sparkfun/SparkFun_DataLogger_IoT_9DoF/Examples/Hardware_Tests/05_MAX17048/05_MAX17048.ino

// SparkFun DataLogger IoT – 9DoF Test Example
// Tested with Espressif ESP32 v2.0.5 and the "ESP32 Dev Module" board definition

/**********************************************************************************************
 *
 * WARNING!
 * 
 * This is a sketch we wrote to test the DataLogger IoT – 9DoF hardware.
 * Please think very carefully before uploading it to your DataLogger.
 * 
 * You will overwrite the DataLogger firmware, leaving it unable to update or restore itself. 
 * 
 * The DataLogger IoT – 9DoF comes pre-programmed with amazing firmware which can do _so_ much.
 * It is designed to be able to update itself and restore itself if necessary.
 * But it can not do that if you overwrite the firmware with this test sketch.
 * It is just like erasing the restore partition on your computer hard drive.
 * Do not do it - unless you really know what you are doing.
 * 
 * Really. We mean it.
 * 
 * Your friends at SparkFun.
 * 
 * License: MIT. Please see LICENSE.MD for more details
 * 
 **********************************************************************************************/

#include <Wire.h> // Needed for I2C

#include <SparkFun_MAX1704x_Fuel_Gauge_Arduino_Library.h> // Click here to get the library: http://librarymanager/All#SparkFun_MAX1704x_Fuel_Gauge_Arduino_Library

SFE_MAX1704X lipo(MAX1704X_MAX17048); // Create a MAX17048

void setup()
{
	Serial.begin(115200); // Start serial, to output debug data
  while (!Serial)
    ; //Wait for user to open terminal
  Serial.println(F("MAX17048 Example"));

  Wire.begin();

  lipo.enableDebugging(); // Uncomment this line to enable helpful debug messages on Serial

  // Set up the MAX17048 LiPo fuel gauge:
  if (lipo.begin() == false) // Connect to the MAX17048 using the default wire port
  {
    Serial.println(F("MAX17048 not detected. Please check wiring. Freezing."));
    while (1)
      ;
  }

  // Just because we can, let's reset the MAX17048
  Serial.println(F("Resetting the MAX17048..."));
  delay(1000); // Give it time to get its act back together

  // Read and print the reset indicator
  Serial.print(F("Reset Indicator was: "));
  bool RI = lipo.isReset(true); // Read the RI flag and clear it automatically if it is set
  Serial.println(RI); // Print the RI
  // If RI was set, check it is now clear
  if (RI)
  {
    Serial.print(F("Reset Indicator is now: "));
    RI = lipo.isReset(); // Read the RI flag
    Serial.println(RI); // Print the RI    
  }

  // To quick-start or not to quick-start? That is the question!
  // Read the following and then decide if you do want to quick-start the fuel gauge.
  // "Most systems should not use quick-start because the ICs handle most startup problems transparently,
  //  such as intermittent battery-terminal connection during insertion. If battery voltage stabilizes
  //  faster than 17ms then do not use quick-start. The quick-start command restarts fuel-gauge calculations
  //  in the same manner as initial power-up of the IC. If the system power-up sequence is so noisy that the
  //  initial estimate of SOC has unacceptable error, the system microcontroller might be able to reduce the
  //  error by using quick-start."
  // If you still want to try a quick-start then uncomment the next line:
	//lipo.quickStart();

  // Read and print the device ID
  Serial.print(F("Device ID: 0x"));
  uint8_t id = lipo.getID(); // Read the device ID
  if (id < 0x10) Serial.print(F("0")); // Print the leading zero if required
  Serial.println(id, HEX); // Print the ID as hexadecimal

  // Read and print the device version
  Serial.print(F("Device version: 0x"));
  uint8_t ver = lipo.getVersion(); // Read the device version
  if (ver < 0x10) Serial.print(F("0")); // Print the leading zero if required
  Serial.println(ver, HEX); // Print the version as hexadecimal

  // Read and print the battery threshold
  Serial.print(F("Battery empty threshold is currently: "));
  Serial.print(lipo.getThreshold());
  Serial.println(F("%"));

  // Read and print the high voltage threshold
  Serial.print(F("High voltage threshold is currently: "));
  float highVoltage = ((float)lipo.getVALRTMax()) * 0.02; // 1 LSb is 20mV. Convert to Volts.
  Serial.print(highVoltage, 2);
  Serial.println(F("V"));

  // Read and print the low voltage threshold
  Serial.print(F("Low voltage threshold is currently: "));
  float lowVoltage = ((float)lipo.getVALRTMin()) * 0.02; // 1 LSb is 20mV. Convert to Volts.
  Serial.print(lowVoltage, 2);
  Serial.println(F("V"));
}

void loop()
{
  // Print the variables:
  Serial.print("Voltage: ");
  Serial.print(lipo.getVoltage());  // Print the battery voltage
  Serial.print("V");

  Serial.print(" Percentage: ");
  Serial.print(lipo.getSOC(), 2); // Print the battery state of charge with 2 decimal places
  Serial.print("%");

  Serial.print(" Change Rate: ");
  Serial.print(lipo.getChangeRate(), 2); // Print the battery change rate with 2 decimal places
  Serial.print("%/hr");

  Serial.println();

  delay(500);
}
